espena/dual-button-doorbell/firmware/dual-button-doorbell/main/components/wifi.cpp

/*
 *  This file is part of the dual-button doorbell project.
 *  Copyright (C) 2023  Espen Andersen (espenandersen.no)
 *
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
 *  You should have received a copy of the GNU General Public License
 *  along with this program.  If not, see <http://www.gnu.org/licenses/>.
 */

#include "wifi.hpp"
#include <string>
#include <memory.h>
#include <algorithm>
#include "time.h"
#include "esp_wifi.h"
#include "freertos/FreeRTOS.h"
#include "freertos/task.h"
#include "freertos/queue.h"
#include "freertos/event_groups.h"
#include "nvs_flash.h"
#include "esp_system.h"
#include "esp_wifi.h"
#include "esp_event.h"
#include "esp_log.h"

#define WIFI_CONNECTED_BIT BIT0
#define WIFI_FAIL_BIT      BIT1

using namespace espena::components;

const char *wifi::LOG_TAG = "wifi";
const esp_event_base_t wifi::event_base = "WIFI_EVENT";

EventGroupHandle_t wifi::m_wifi_event_group = xEventGroupCreate();

wifi::wifi() {
  m_message_queue = xQueueCreate( 10, sizeof( wifi_task_queue_item ) );
  m_wifi_task_params.instance = this;
  m_wifi_task_params.task_handle = NULL;
  xTaskCreate( &wifi::wifi_task,
               "wifi_task",
               WIFI_TASK_STACK_DEPTH,
               &m_wifi_task_params,
               configMAX_PRIORITIES - 1,
               &m_wifi_task_params.task_handle );
}

wifi::~wifi() {

}

void wifi::wifi_task( void *arg ) {
  wifi_task_params *params = static_cast<wifi_task_params *>( arg );
  wifi *inst = params->instance;
  wifi_task_queue_item item;
  while( 1 ) {
    if( xQueueReceive( inst->m_message_queue, &item, portMAX_DELAY ) ) {
      inst->on_message( item.message, item.arg );
    }
  }
}

void wifi::set_event_loop_handle( esp_event_loop_handle_t event_loop_handle ) {
  m_event_dispatcher.set_event_loop_handle( event_loop_handle );
}

void wifi::add_event_listener( event_id event_id,
                                esp_event_handler_t event_handler )
{
  m_event_dispatcher.add_event_listener( wifi::event_base,
                                          event_id,
                                          event_handler );
}

void wifi::on_message( wifi_task_message msg, void *arg ) {
  switch( msg ) {
    case wifi_connect:
      connect();
      break;
  }
}

void wifi::event_handler( void *arg,
                          esp_event_base_t event_base,
                          int32_t event_id,
                          void *event_data )
{
  static int retries = 0;
  wifi *instance = static_cast<wifi *>( arg );
  if( event_base == WIFI_EVENT ) {
    switch( event_id ) {
      case WIFI_EVENT_STA_START:
        esp_wifi_connect();
        break;
      case WIFI_EVENT_STA_DISCONNECTED:
        if( retries++ < MAX_RETRIES ) {
          vTaskDelay( 1000 / portTICK_PERIOD_MS );
          esp_wifi_connect();
          ESP_LOGI( LOG_TAG, "Retry connection to network %d of %d", retries, MAX_RETRIES );
        }
        else {
          ESP_LOGE( LOG_TAG, "Unable to connect to WiFi network %s", instance->m_ssid.c_str() );
          xEventGroupSetBits( m_wifi_event_group, WIFI_FAIL_BIT );
        }
        break;
    }
  }
  else if( event_base == IP_EVENT ) {
    switch( event_id ) {
      case IP_EVENT_STA_GOT_IP:
        ip_event_got_ip_t *e = static_cast<ip_event_got_ip_t *>( event_data );
        ESP_LOGI( LOG_TAG, "Got ip:" IPSTR, IP2STR( &( e->ip_info.ip ) ) );
        retries = 0;
        xEventGroupSetBits( m_wifi_event_group, WIFI_CONNECTED_BIT );
        instance->m_event_dispatcher.dispatch( wifi::event_base, ON_WIFI_CONNECTED, arg, 0 );
        break;
    }
  }
}

void wifi::connect( std::string ssid,
                    std::string password )
{
  m_ssid = ssid;
  m_password = password;
  ESP_LOGI( LOG_TAG, "Using SSID %s and PASSWORD %s", m_ssid.c_str(), m_password.c_str() );
  wifi_task_queue_item item = {
    .message = wifi_connect,
    .arg = this
  };
  xQueueSend( m_message_queue, &item, 1 );
}

void wifi::connect( void ) {

    ESP_LOGI( LOG_TAG, "start wifi connect thread" );

    esp_err_t ret = nvs_flash_init();
    if ( ret == ESP_ERR_NVS_NO_FREE_PAGES ||
        ret == ESP_ERR_NVS_NEW_VERSION_FOUND )
    {
      ESP_LOGI( LOG_TAG, "Erasing NVS mem" );
      ESP_ERROR_CHECK( nvs_flash_erase() );
      ret = nvs_flash_init();
    }  

    ESP_LOGI( LOG_TAG, "Calling esp_wifi_init" );

    wifi_init_config_t config = WIFI_INIT_CONFIG_DEFAULT();
    esp_wifi_init( &config );

    ESP_LOGI( LOG_TAG, "Calling esp_wifi_set_mode" );
    esp_wifi_set_mode( WIFI_MODE_STA );

    ESP_LOGI( LOG_TAG, "Calling esp_netif_init" );
    esp_netif_init();

    ESP_LOGI( LOG_TAG, "Calling esp_event_loop_create_default" );
    esp_event_loop_create_default();

    ESP_LOGI( LOG_TAG, "Calling esp_netif_create_default_wifi_sta" );
    esp_netif_create_default_wifi_sta();

    wifi_init_config_t wifi_ini = WIFI_INIT_CONFIG_DEFAULT();
    ESP_LOGI( LOG_TAG, "Calling esp_wifi_init" );
    esp_wifi_init( &wifi_ini );

    ESP_LOGI( LOG_TAG, "Register event handler for any ID" );
    esp_event_handler_instance_t instance_any_id;
    esp_event_handler_instance_register( WIFI_EVENT,
                                        ESP_EVENT_ANY_ID,
                                        &event_handler,
                                        this,
                                        &instance_any_id );

    ESP_LOGI( LOG_TAG, "Register event handler for IP event" );
    esp_event_handler_instance_t instance_got_ip;
    esp_event_handler_instance_register( IP_EVENT,
                                        IP_EVENT_STA_GOT_IP,
                                        &event_handler,
                                        this,
                                        &instance_got_ip );


    ESP_LOGI( LOG_TAG, "Fetch SSID and password" );
    wifi_config_t wifi_cfg;
    memset( &wifi_cfg, 0x00u, sizeof( wifi_config_t ) );

    const size_t n_ssid = sizeof( wifi_cfg.sta.ssid );
    const size_t n_password = sizeof( wifi_cfg.sta.password );

    ESP_LOGI( LOG_TAG, "ssid: %s passwd: %s", wifi_cfg.sta.ssid, wifi_cfg.sta.password );

    strncpy( ( char * ) &wifi_cfg.sta.ssid, m_ssid.c_str(), n_ssid - 1 );
    strncpy( ( char * ) &wifi_cfg.sta.password, m_password.c_str(), n_password - 1 );

    wifi_cfg.sta.threshold.authmode = WIFI_AUTH_WPA2_PSK;
    wifi_cfg.sta.sae_pwe_h2e = WPA3_SAE_PWE_UNSPECIFIED;

    ESP_LOGI( LOG_TAG, "Calling esp_wifi_set_mode" );
    esp_wifi_set_mode( WIFI_MODE_STA );

    ESP_LOGI( LOG_TAG, "Calling esp_wifi_set_config" );
    esp_wifi_set_config( WIFI_IF_STA, &wifi_cfg );

    ESP_LOGI( LOG_TAG, "Calling esp_wifi_start" );
    esp_wifi_start();

    ESP_LOGI( LOG_TAG, "Calling xEventGroupWaitBits" );
    EventBits_t bits = xEventGroupWaitBits( m_wifi_event_group,
                                            WIFI_CONNECTED_BIT | WIFI_FAIL_BIT,
                                            pdFALSE,
                                            pdFALSE,
                                            portMAX_DELAY );

}
