espena/dual-button-doorbell/firmware/dual-button-doorbell/main/components/ntp.cpp

/*
 *  This file is part of the dual-button doorbell project.
 *  Copyright (C) 2023  Espen Andersen (espenandersen.no)
 *
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
 *  You should have received a copy of the GNU General Public License
 *  along with this program.  If not, see <http://www.gnu.org/licenses/>.
 */

#include "ntp.hpp"
#include "memory.h"
#include "time.h"
#include "esp_netif_sntp.h"
#include "esp_event.h"
#include "esp_log.h"

using namespace espena::components;

const char *ntp::LOG_TAG = "ntp";
const esp_event_base_t ntp::event_base = "NTP_EVENT";

ntp::ntp( const ntp::configuration &config ) :
  m_config( config ), // Defaults
  m_time_updated( false )
{
  ESP_LOGI( LOG_TAG, "Server is %s", m_config.server.c_str() );
  ESP_LOGI( LOG_TAG, "Timezone is %s", m_config.timezone.c_str() );
  m_message_queue = xQueueCreate( 10, sizeof( ntp_task_queue_item ) );
  m_ntp_task_params.instance = this;
  m_ntp_task_params.task_handle = NULL;
  xTaskCreate( &ntp::ntp_task,
               "ntp_task",
               NTP_TASK_STACK_DEPTH,
               &m_ntp_task_params,
               2,
               &m_ntp_task_params.task_handle );
}

ntp::~ntp() {

}

void ntp::set_event_loop_handle( esp_event_loop_handle_t event_loop_handle ) {
  m_event_dispatcher.set_event_loop_handle( event_loop_handle );
}

void ntp::add_event_listener( event_id event_id,
                              esp_event_handler_t event_handler )
{
  m_event_dispatcher.add_event_listener( ntp::event_base,
                                         event_id,
                                         event_handler );
}

void ntp::ntp_task( void *arg ) {
  ntp_task_params *params = static_cast<ntp_task_params *>( arg );
  ntp *inst = params->instance;
  ntp_task_queue_item item;
  while( 1 ) {
    if( xQueueReceive( inst->m_message_queue, &item, portMAX_DELAY ) ) {
      inst->on_message( item.message, item.arg );
    }
  }
}

void ntp::on_message( ntp_task_message msg, void *arg ) {
  switch( msg ) {
    case ntp_update:
      time_update();
      break;
  }
}

void ntp::init( const std::string server,
                const std::string timezone )
{
  // Do not overwrite defaults with empty user settings
  if( !server.empty() ) m_config.server = server;
  if( !timezone.empty() ) m_config.timezone = timezone;
}

void ntp::time_update_async() {
  ntp_task_queue_item item = {
    .message = ntp_update,
    .arg = this
  };
  xQueueSend( m_message_queue, &item, 1 );
}

void ntp::time_update() {
  esp_netif_sntp_deinit();
  esp_sntp_config_t sntp_config = ESP_NETIF_SNTP_DEFAULT_CONFIG( m_config.server.c_str() );
  esp_netif_sntp_init( &sntp_config );
  if( esp_netif_sntp_sync_wait( pdMS_TO_TICKS( 20000 ) ) != ESP_OK ) {
    ESP_LOGW( LOG_TAG, "Failed to update system time within 20s timeout" );
  }
  else {
    m_event_dispatcher.dispatch( ntp::event_base, ON_NTP_TIME_UPDATED, NULL, 0 );
    m_time_updated = true;
    const char *tz = m_config.timezone.c_str();
    setenv( "TZ", tz, 1 );
    tzset();
    time_t t = time( NULL );
    tm *now = localtime( &t );
    char timestr[ 100 ];
    memset( &timestr, 0x00, sizeof( timestr ) );
    strftime( timestr, sizeof( timestr ) - 1, "%Y-%m-%d %H:%M:%S", now );
    ESP_LOGI( LOG_TAG, "Time zone set to %s: %s", tz, timestr );
  }

}
