espena/dual-button-doorbell/firmware/dual-button-doorbell/main/components/sound.cpp

/*
 *  This file is part of the dual-button doorbell project.
 *  Copyright (C) 2023  Espen Andersen (espenandersen.no)
 *
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
 *  You should have received a copy of the GNU General Public License
 *  along with this program.  If not, see <http://www.gnu.org/licenses/>.
 */

#include "sound.hpp"
#include "esp_log.h"
#include "esp_event.h"
#include "memory.h"
#include "driver/gpio.h"
#include "driver/i2s_std.h"
#include "../dummy_sound.h"
#include "../io.h"

using namespace espena::components;

const char *sound::LOG_TAG = "sound";
const esp_event_base_t sound::event_base = "SOUND_EVENT";

sound::sound( const sound::configuration &config ) :
  m_stop( false ),
  m_playing( false ),
  m_config( config ),
  m_i2s_std_cfg( {
    .clk_cfg = I2S_STD_CLK_DEFAULT_CONFIG( 44100 ),
    .slot_cfg = I2S_STD_MSB_SLOT_DEFAULT_CONFIG( I2S_DATA_BIT_WIDTH_16BIT, I2S_SLOT_MODE_MONO ),
    .gpio_cfg = {
      .mclk = I2S_GPIO_UNUSED,
      .bclk = config.gpio_i2s_bclk,
      .ws = config.gpio_i2s_lrclk,
      .dout = config.gpio_i2s_dout,
      .din = I2S_GPIO_UNUSED,
      .invert_flags = {
        .mclk_inv = false,
        .bclk_inv = false,
        .ws_inv = false
      }
    }
  } )
{
  m_message_queue = xQueueCreate( 10, sizeof( sound_task_queue_item ) );
  m_sound_task_params.instance = this;
  m_sound_task_params.task_handle = NULL;
  xTaskCreate( &sound::sound_task,
               "sound_task",
               SOUND_TASK_STACK_DEPTH,
               &m_sound_task_params,
               2,
               &m_sound_task_params.task_handle );
  initialize();
}

sound::~sound() {

}

void sound::initialize() {
  gpio_reset_pin( m_config.gpio_i2s_sd_mode );
  gpio_set_direction( m_config.gpio_i2s_sd_mode, GPIO_MODE_OUTPUT );
  i2s_chan_config_t chan_cfg = I2S_CHANNEL_DEFAULT_CONFIG( I2S_NUM_0, I2S_ROLE_MASTER );
  i2s_new_channel( &chan_cfg, &m_i2s_tx_handle, NULL );
  i2s_channel_init_std_mode( m_i2s_tx_handle, &m_i2s_std_cfg );
}

void sound::sound_task( void *arg ) {
  sound_task_params *params = static_cast<sound_task_params *>( arg );
  sound *inst = params->instance;
  sound_task_queue_item item;
  while( 1 ) {
    if( xQueueReceive( inst->m_message_queue, &item, portMAX_DELAY ) ) {
      inst->on_message( item.message, item.arg );
    }
  }
}

void sound::on_message( sound_task_message msg, void *arg ) {
  switch( msg ) {
    case sound_play:
      play( static_cast<FILE *>( arg ) );
      break;
  }
}

void sound::play_async( FILE *fp ) {
  while( m_playing ) {
    vTaskDelay( 1 );
  }
  sound_task_queue_item item = {
    .message = sound_play,
    .arg = fp
  };
  xQueueSend( m_message_queue, &item, 1 );  
}

void sound::stop_async() {
  while( !m_stop ) m_stop = true;
}

void sound::play( FILE *fp ) {
  m_playing = true;
  while( m_stop ) m_stop = false;
  static const size_t BUFFER_SIZE = 1024;
  if( fp ) {
    wave_hdr wh;
    fread( ( void * ) &wh, sizeof( wh ), 1, fp );
    ESP_LOGI( LOG_TAG, "Wave file has data chunk size %lu", wh.w_datachunksize );
    if( memcmp( wh.w_fileid, ( void * ) "RIFF", 4 ) != 0 ||
        memcmp( wh.w_waveid, ( void * ) "WAVE", 4 ) != 0 ||
        memcmp( wh.w_fmtid, ( void * ) "fmt ", 4 ) != 0 )
    {
      return;
    }
    i2s_channel_enable( m_i2s_tx_handle );
    gpio_set_level( m_config.gpio_i2s_sd_mode, 1 );
    char buf[ BUFFER_SIZE ];
    size_t bytes_left_to_write = wh.w_datachunksize;
    do {
      size_t chunk_size = fread( ( void * ) buf, 1, sizeof( buf ) / sizeof( buf[ 0 ] ), fp );
      if( chunk_size > bytes_left_to_write ) {
        chunk_size = bytes_left_to_write;
        fseek( fp, 0, SEEK_END ); // Reach end of data chunk, skip footer
      }
      bytes_left_to_write -= chunk_size;
      size_t bytes_written = 0;
      while( !m_stop && bytes_written < chunk_size ) {
        i2s_channel_write( m_i2s_tx_handle,
                           buf,
                           chunk_size,
                           &bytes_written,
                           5000 );
      }
      vTaskDelay( 1 );
    } while( !m_stop && !feof( fp ) ); 
    i2s_channel_disable( m_i2s_tx_handle );
    m_event_dispatcher.dispatch( sound::event_base,
                                 ON_PLAY_END,
                                 &fp,
                                 sizeof( FILE * ) );
  }
  m_playing = false;
}

void sound::set_event_loop_handle( esp_event_loop_handle_t event_loop_handle ) {
  m_event_dispatcher.set_event_loop_handle( event_loop_handle );
}

void sound::add_event_listener( event_id event_id,
                                esp_event_handler_t event_handler )
{
  m_event_dispatcher.add_event_listener( sound::event_base,
                                          event_id,
                                          event_handler );
}
