espena/dual-button-doorbell/firmware/dual-button-doorbell/main/components/settings_file.hpp

/*
 *  This file is part of the dual-button doorbell project.
 *  Copyright (C) 2023  Espen Andersen (espenandersen.no)
 *
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
 *  You should have received a copy of the GNU General Public License
 *  along with this program.  If not, see <http://www.gnu.org/licenses/>.
 */

#ifndef __settings_file_hpp__
#define __settings_file_hpp__

#include <string>
#include <vector>
#include <cstdio>
#include "cJSON.h"

namespace espena::components {

  class settings_file {

    public:

      typedef struct clip_override_struct {
        int enable;
        std::string name;
        std::string from;
        time_t duration;
        std::string clip;
      } clip_override;

    private:

      static const char *LOG_TAG;

      cJSON *m_root;

      void fetch_button_properties( cJSON *, std::string & );
      void fetch_default_clip( cJSON *, std::string & );
      void fetch_silent_clip( cJSON *, int &, std::string &, std::string &, time_t & );
      void fetch_clip_overrides( cJSON *, std::vector<clip_override> & );
      void fetch_bell_settings( cJSON *, int &, int & );
      void fetch_wifi_settings( cJSON *, std::string &, std::string & );
      void fetch_ntp_settings( cJSON *, std::string &, std::string & );
      void fetch_mqtt_settings( cJSON *, int &, std::string &, std::string &, std::string & );
      void fetch_logger_settings( cJSON *, size_t & );

      void update();

      void debug_output();
    
    public:

      std::string m_button_label[ 2 ];
      std::string m_button_default_clip[ 2 ];
      std::string m_button_silent_clip[ 2 ];
      std::string m_button_silent_from[ 2 ];
      int m_button_silent_enable[ 2 ];
      time_t m_button_silent_duration[ 2 ];
      int m_button_bell_count[ 2 ];
      int m_button_bell_delay[ 2 ];

      std::vector<clip_override> m_button_overrides[ 2 ];

      std::string m_wifi_ssid;
      std::string m_wifi_password;

      std::string m_ntp_server;
      std::string m_ntp_timezone;

      int m_mqtt_enable;
      std::string m_mqtt_server;
      std::string m_mqtt_cert_file;
      std::string m_mqtt_topic;

      size_t m_logger_max_file_size_mb;

      settings_file();
      ~settings_file();
  
      void load( FILE * settings_json );
      void write( FILE * settings_json );

  }; // class settings_file

}; // namespace espena::components

#endif // __settings_file_hpp__
